kholia/pico-cw-beacon-drs/references/QDX-1.png

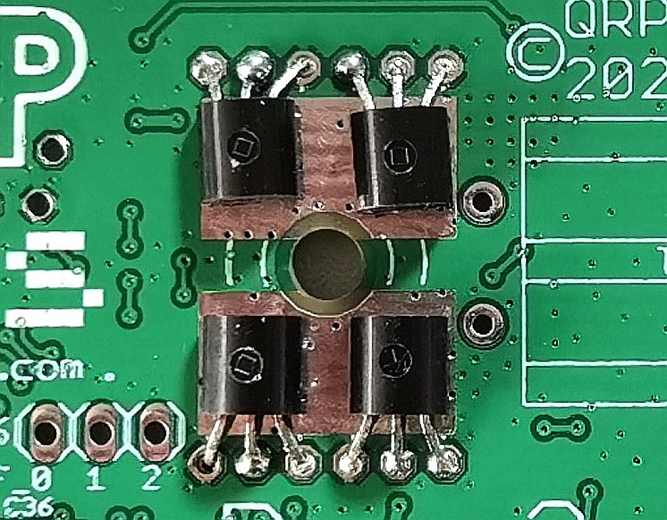
references/QDX-1.png
