kholia/pico-cw-beacon-drs/references/QDX-2.png

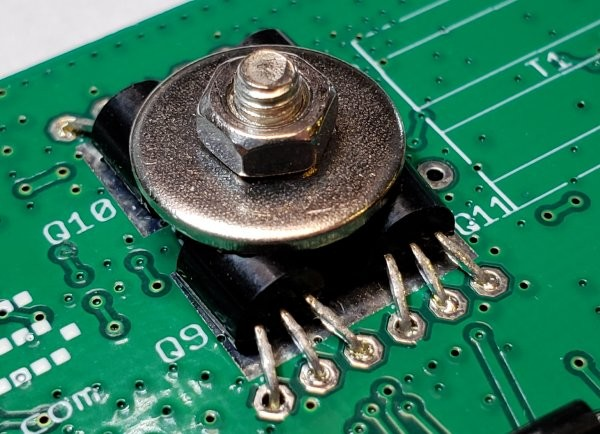
references/QDX-2.png
