kholia/pico-cw-beacon-drs/references/qrp-rf-amp4.jpg

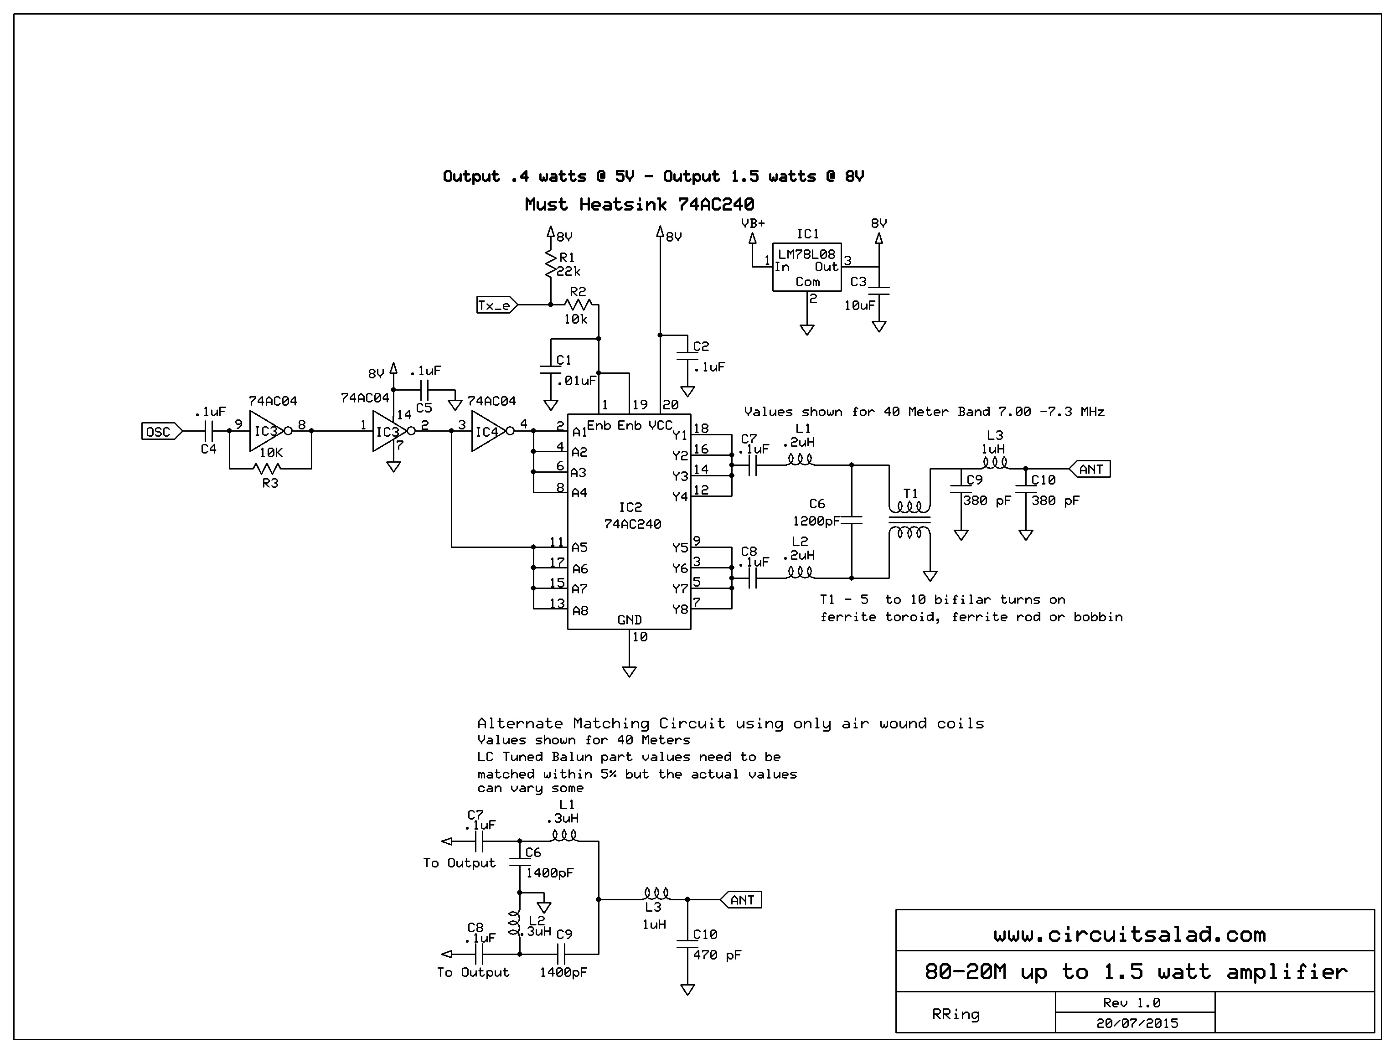
references/qrp-rf-amp4.jpg
