kholia/pico-cw-beacon-drs/Screenshot_2022-10-02_15-56-46.png

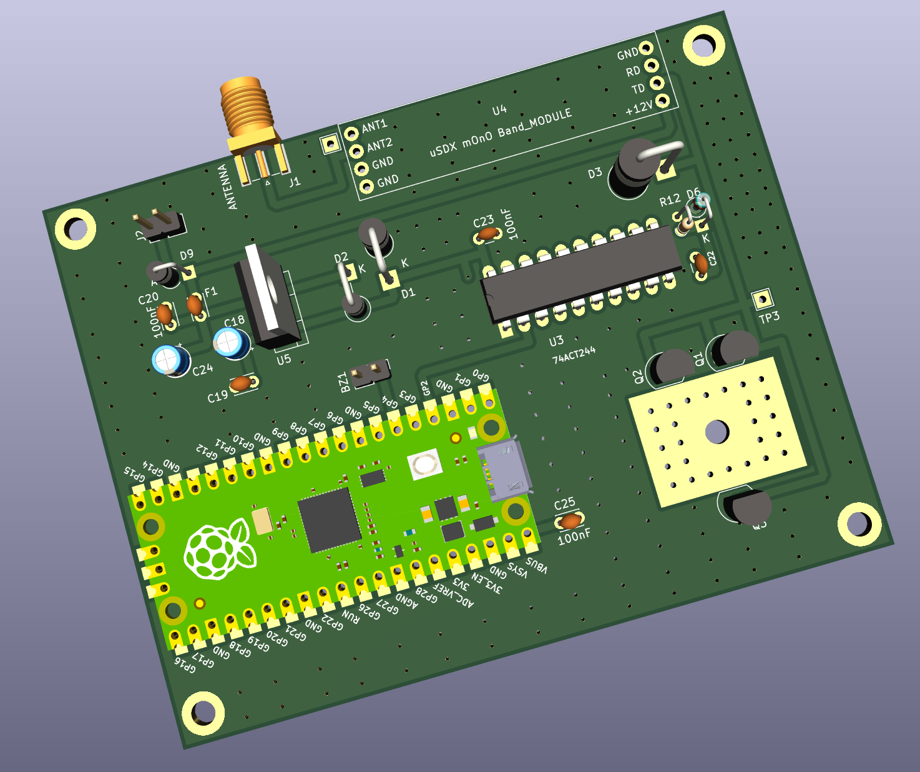
Screenshot_2022-10-02_15-56-46.png
