kholia/pico-cw-beacon-drs/Screenshot_2022-10-07_15-12-50.png

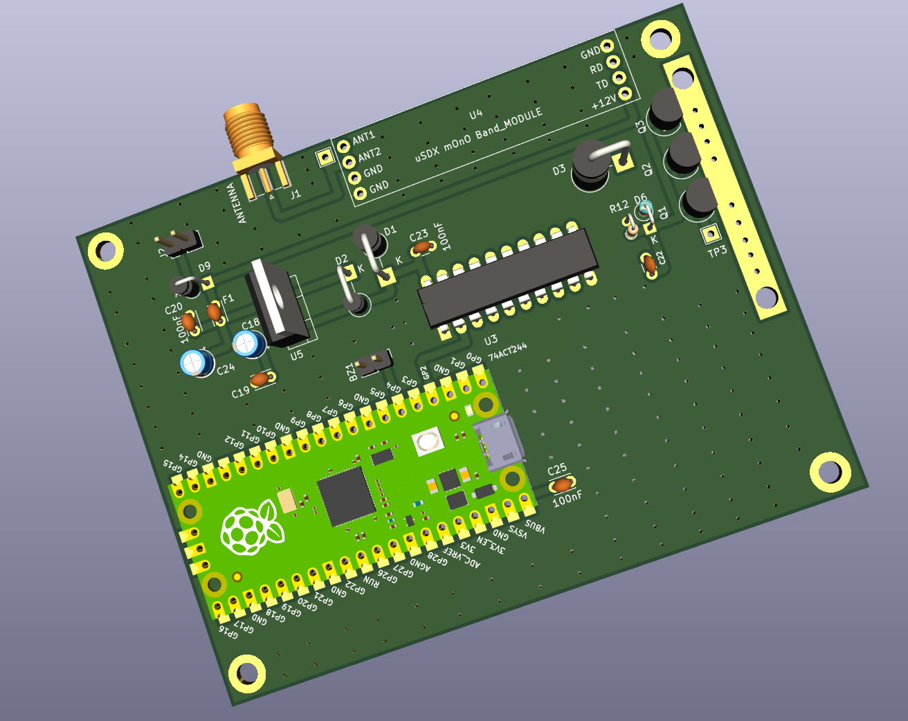
Screenshot_2022-10-07_15-12-50.png
