kholia/pico-cw-beacon-drs/Screenshot_2022-10-08_14-58-00.png

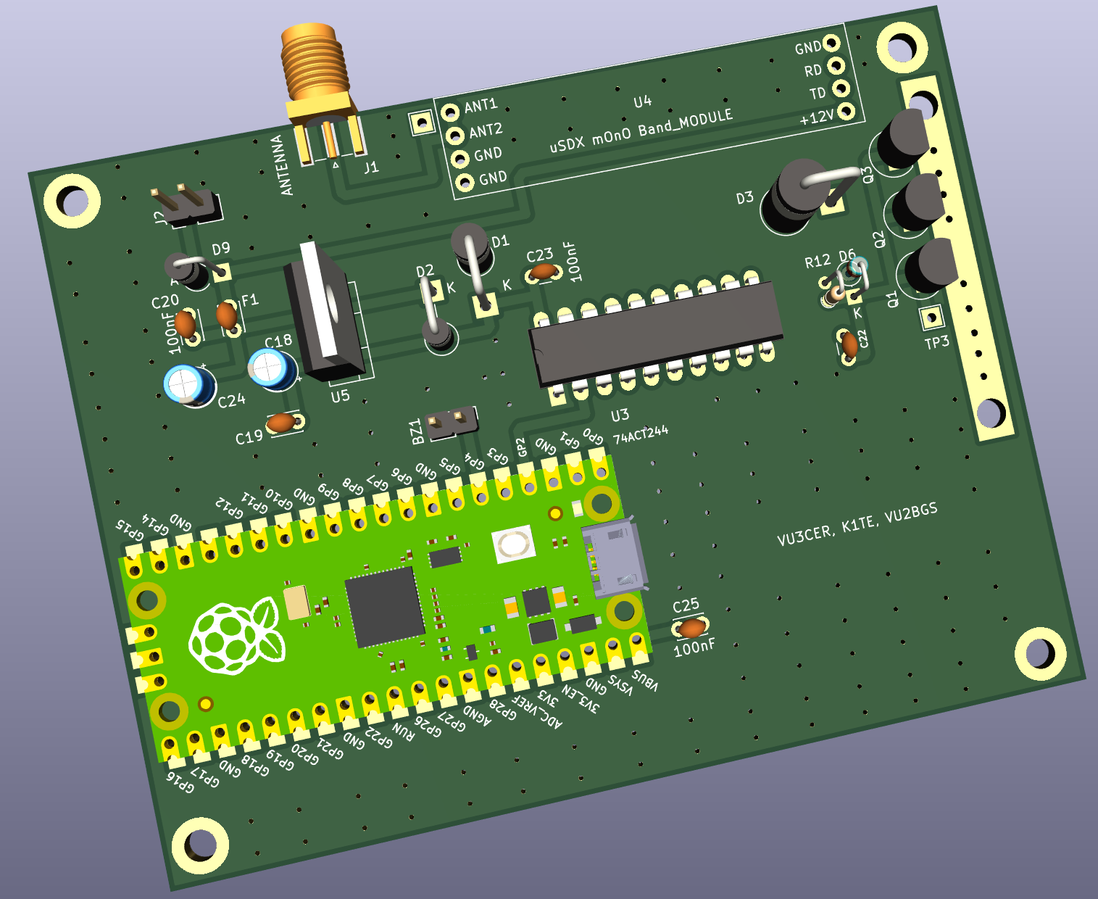
Screenshot_2022-10-08_14-58-00.png
